youdbetterrun/youdbetterrun-3d/step/Main Assembly - Glass.step

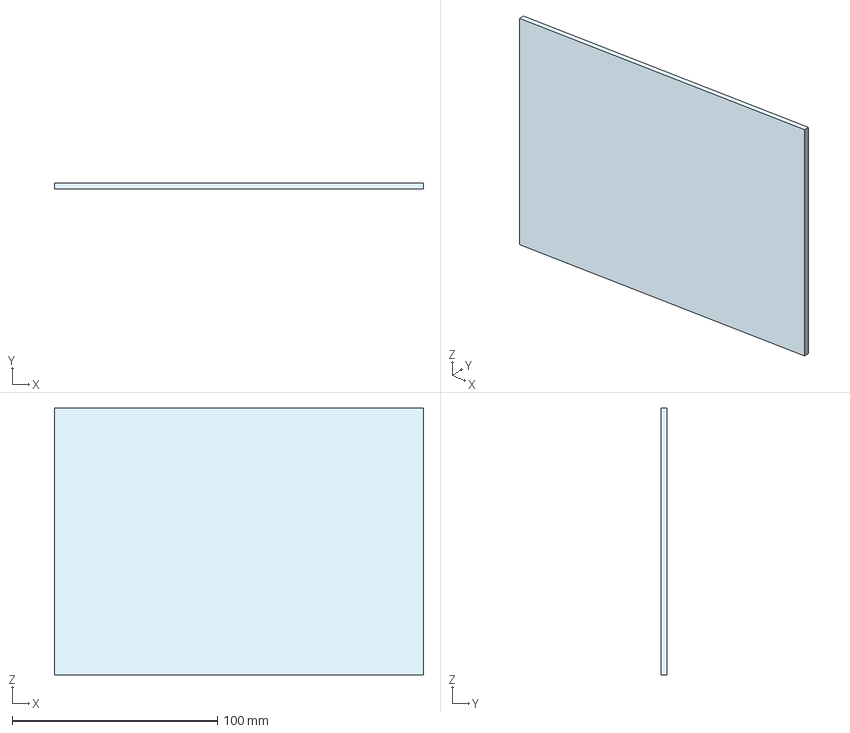
[picture p20: CAD file, 2024-12-17]
step/Main Assembly - Glass.step
180.0 x 3.00 x 130.0 mm
