youdbetterrun/youdbetterrun-3d/step/Main Assembly - Picture Frame.step

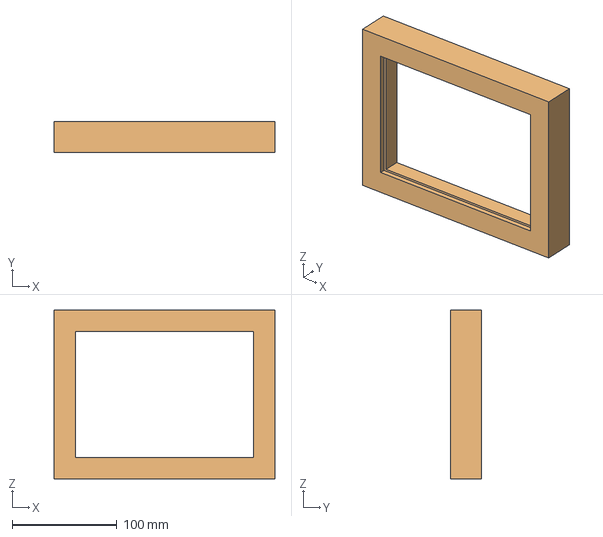
[picture p21: CAD file, 2024-12-17]
step/Main Assembly - Picture Frame.step
211.0 x 30.0 x 161.0 mm
