youdbetterrun/youdbetterrun-3d/step/Main Assembly - SOT_23_5.step

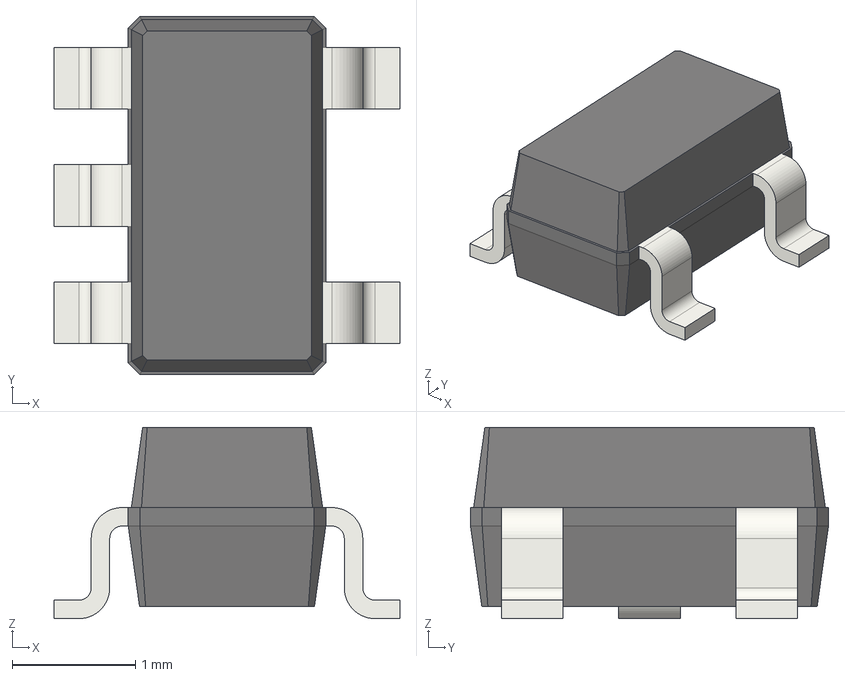
[picture p22: CAD file, 2024-12-17]
step/Main Assembly - SOT_23_5.step
2.80 x 2.90 x 1.55 mm
