youdbetterrun/youdbetterrun-3d/step/Main Assembly - ESP_12E001_cp (37).step

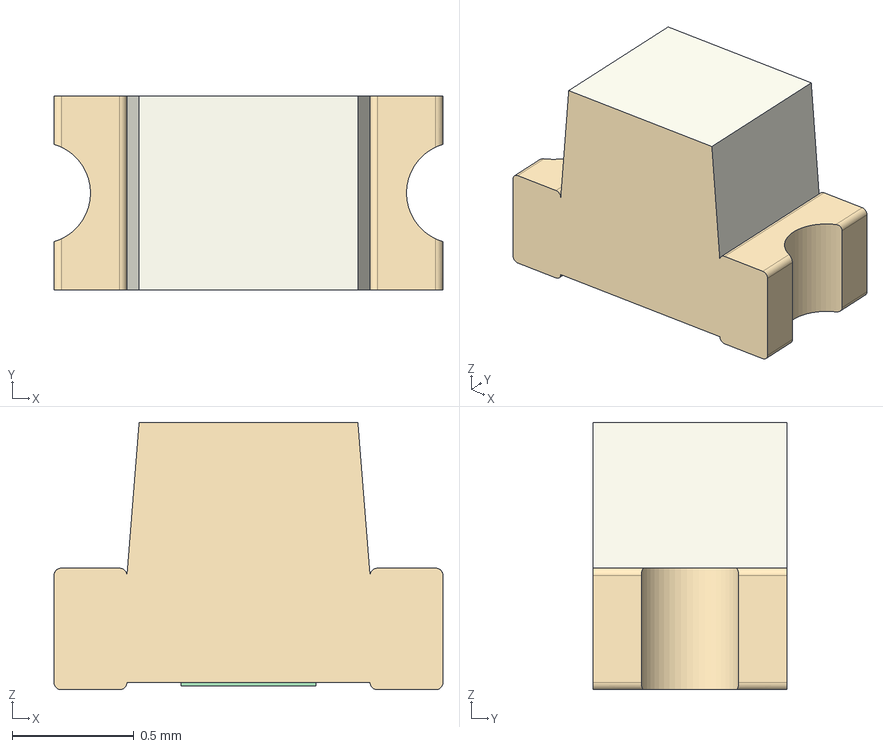
[picture p23: CAD file, 2024-12-17]
step/Main Assembly - ESP_12E001_cp (37).step
1.60 x 0.8 x 1.10 mm
