youdbetterrun/youdbetterrun-3d/step/Main Assembly - QFN-24-1EP_4x4mm_Pitch0.5mm.step

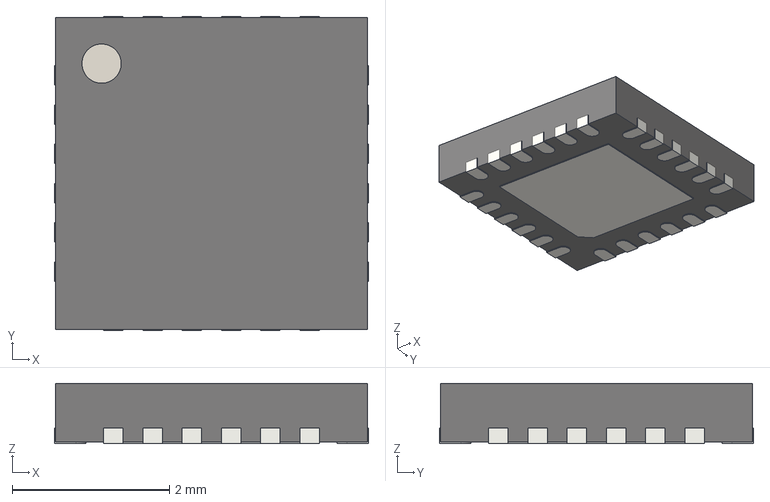
[picture p24: CAD file, 2024-12-17]
step/Main Assembly - QFN-24-1EP_4x4mm_Pitch0.5mm.step
4.00 x 4.00 x 0.77 mm
