youdbetterrun/youdbetterrun-3d/step/Main Assembly - epd.step

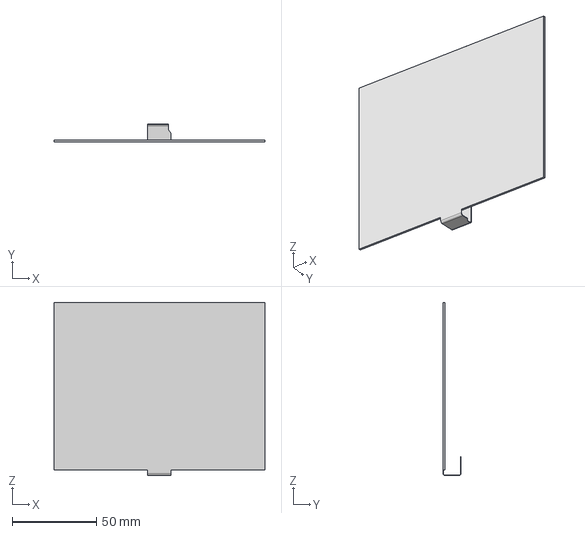
[picture p25: CAD file, 2024-12-17]
step/Main Assembly - epd.step
125.4 x 10.8 x 102.9 mm
