youdbetterrun/youdbetterrun-3d/step/Main Assembly - D_SOD_123.step

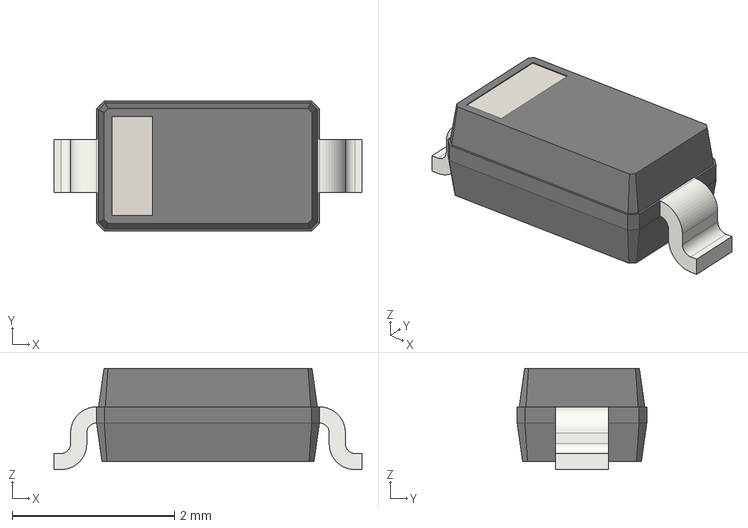
[picture p26: CAD file, 2024-12-17]
step/Main Assembly - D_SOD_123.step
3.80 x 1.60 x 1.25 mm
