youdbetterrun/youdbetterrun-3d/step/Main Assembly - PinHeader_1x10_P254mm_Vertical.step

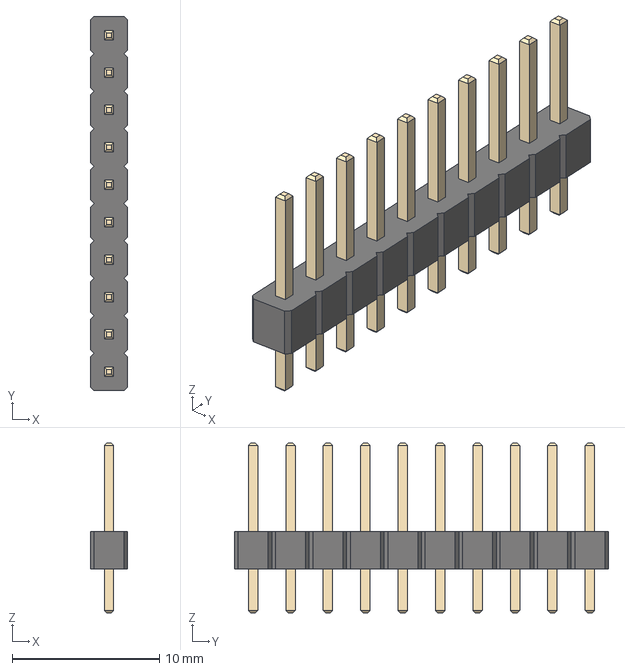
[picture p27: CAD file, 2024-12-17]
step/Main Assembly - PinHeader_1x10_P254mm_Vertical.step
2.54 x 25.4 x 11.5 mm
