youdbetterrun/youdbetterrun-3d/step/Main Assembly - PinHeader_1x12_P254mm_Vertical.step

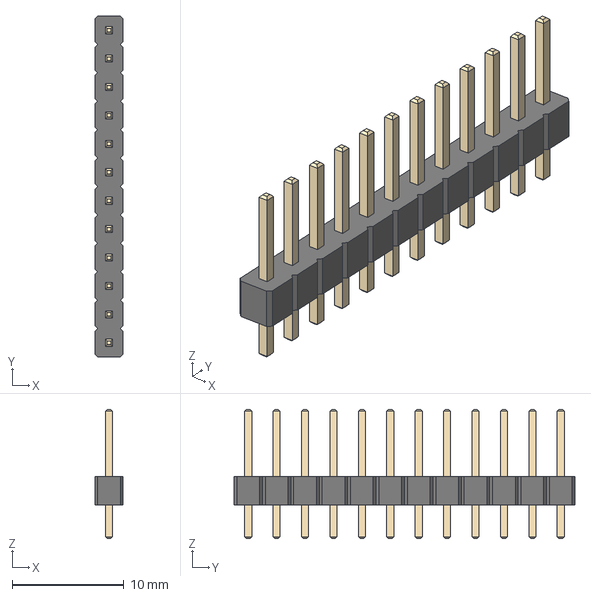
[picture p28: CAD file, 2024-12-17]
step/Main Assembly - PinHeader_1x12_P254mm_Vertical.step
2.54 x 30.5 x 11.5 mm
