youdbetterrun/youdbetterrun-3d/step/Main Assembly - SOT_23.step

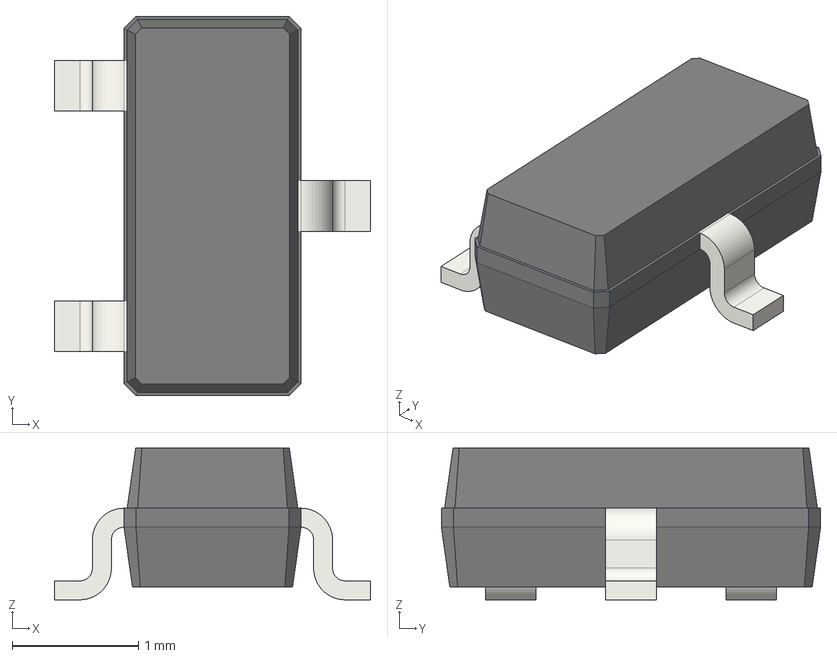
[picture p29: CAD file, 2024-12-17]
step/Main Assembly - SOT_23.step
2.50 x 3.00 x 1.20 mm
