youdbetterrun/youdbetterrun-3d/step/Main Assembly - SOT_323_SC_70.step

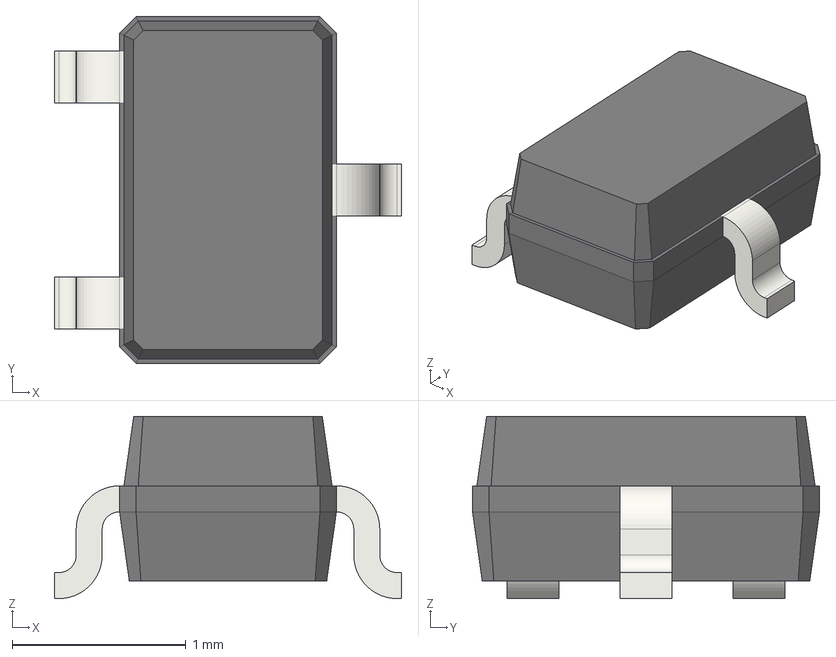
[picture p30: CAD file, 2024-12-17]
step/Main Assembly - SOT_323_SC_70.step
2.00 x 2.00 x 1.05 mm
