youdbetterrun/youdbetterrun-3d/step/Main Assembly - TFT.step

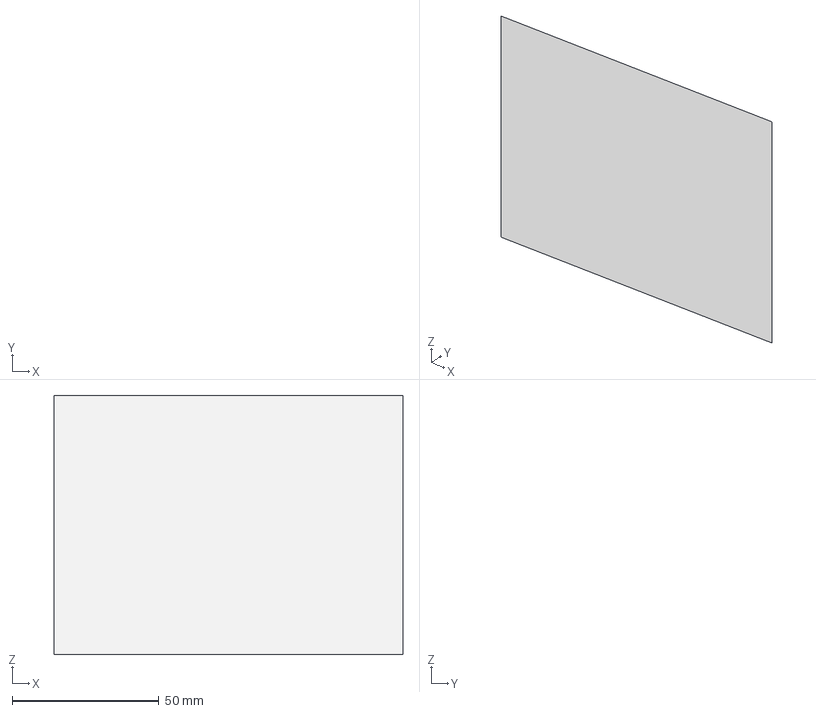
[picture p31: CAD file, 2024-12-17]
step/Main Assembly - TFT.step
118.8 x 0 x 88.2 mm
