youdbetterrun/youdbetterrun-3d/step/Main Assembly - SOT_143.step

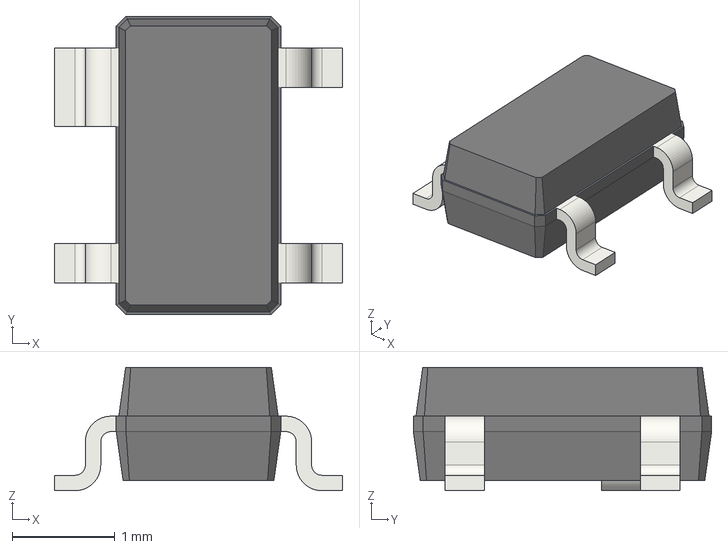
[picture p32: CAD file, 2024-12-17]
step/Main Assembly - SOT_143.step
2.80 x 2.90 x 1.20 mm
